changkaryee/Portable-Polarization-Camera/polar cam Files/Examples/Example of Computer Screen/Screen Dolp.jpg

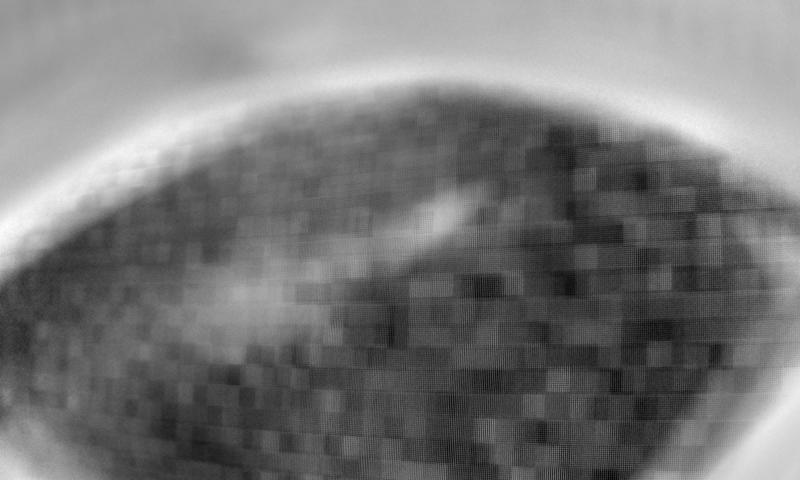
polar cam Files/Examples/Example of Computer Screen/Screen Dolp.jpg
