changkaryee/Portable-Polarization-Camera/polar cam Files/Examples/Example of Lake/Lake Dolp.jpg

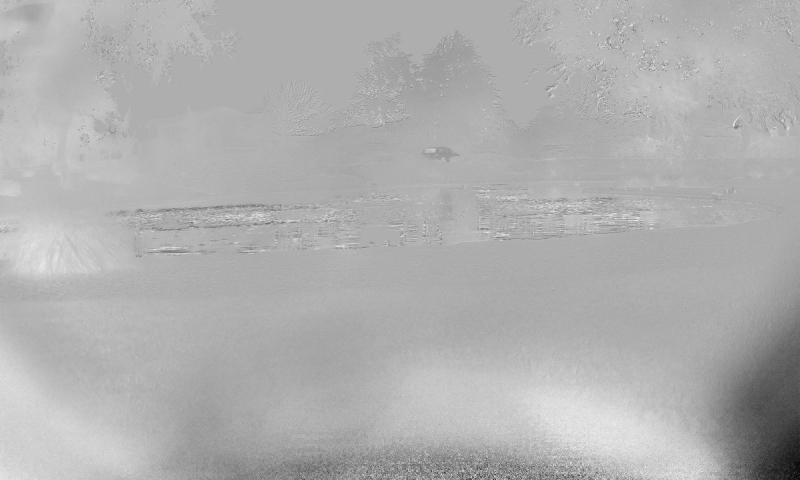
polar cam Files/Examples/Example of Lake/Lake Dolp.jpg
