changkaryee/Portable-Polarization-Camera/polar cam Files/Examples/Example of Lake/Lake S1.jpg

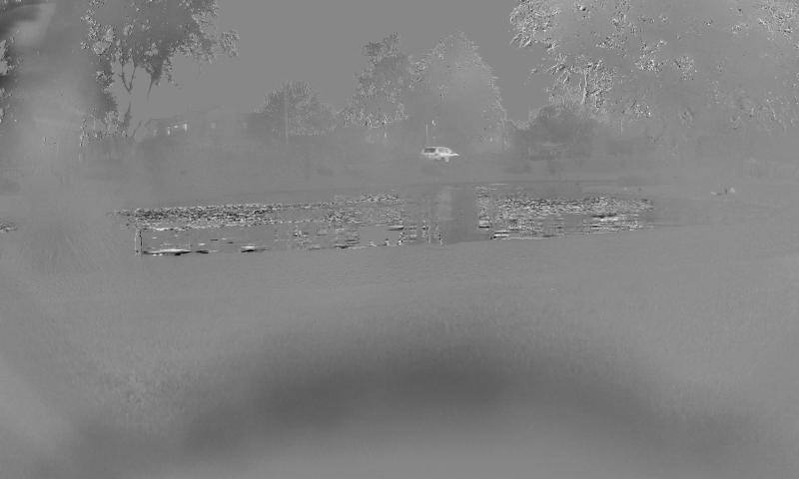
polar cam Files/Examples/Example of Lake/Lake S1.jpg
