changkaryee/Portable-Polarization-Camera/polar cam Files/Examples/Sky.jpg

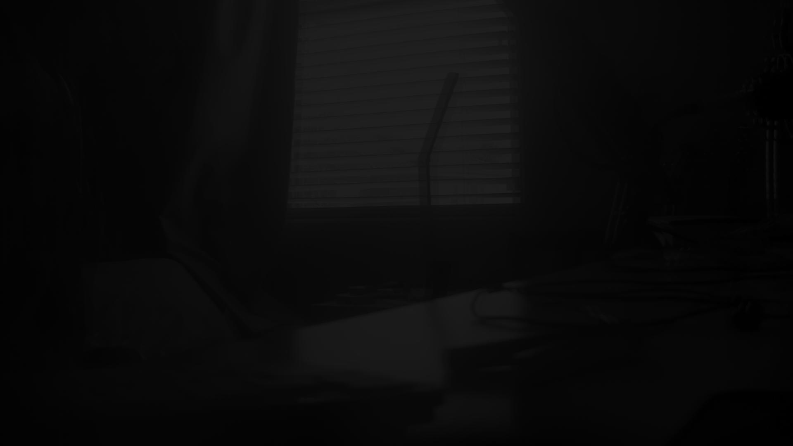
polar cam Files/Examples/Sky.jpg
