changkaryee/Portable-Polarization-Camera/polar cam Files/Pics0/Lake zero.jpg

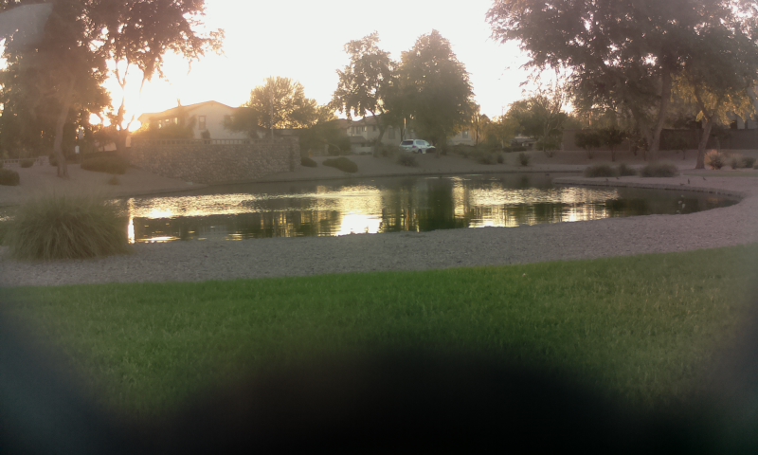
polar cam Files/Pics0/Lake zero.jpg
