changkaryee/Portable-Polarization-Camera/polar cam Files/Pics0/zero.jpg

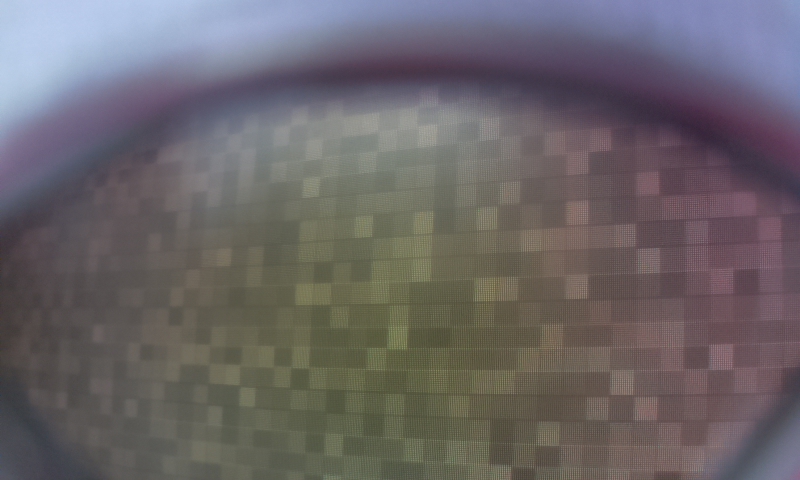
polar cam Files/Pics0/zero.jpg
