changkaryee/Portable-Polarization-Camera/polar cam Files/Pics90/ninety.jpg

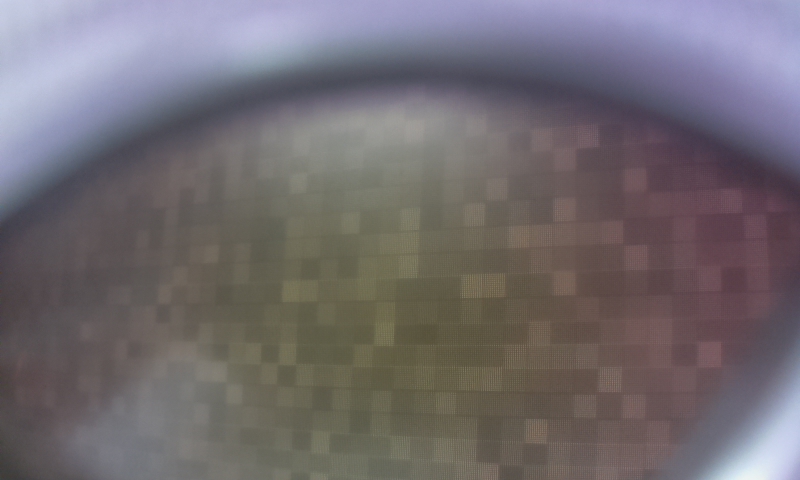
polar cam Files/Pics90/ninety.jpg
