changkaryee/Portable-Polarization-Camera/polar cam Files/Pics135/hundredthirtyfive.jpg

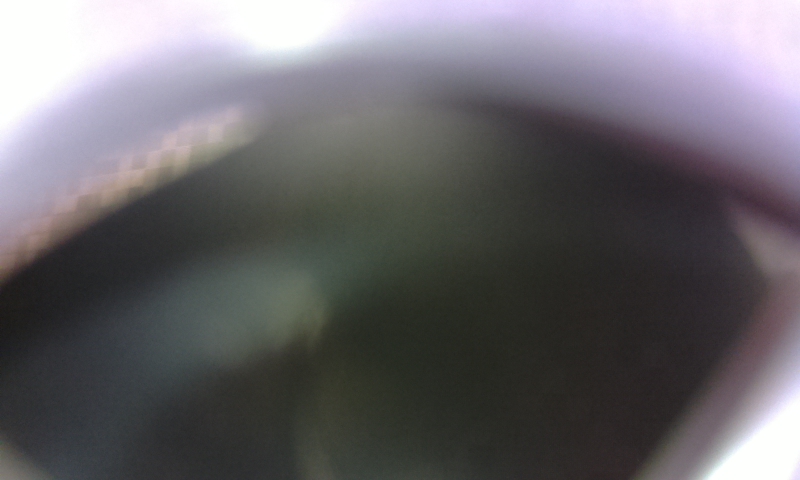
polar cam Files/Pics135/hundredthirtyfive.jpg
